basic-bitch-foundation/HUGINN/images/videoframe_134466 (1).png

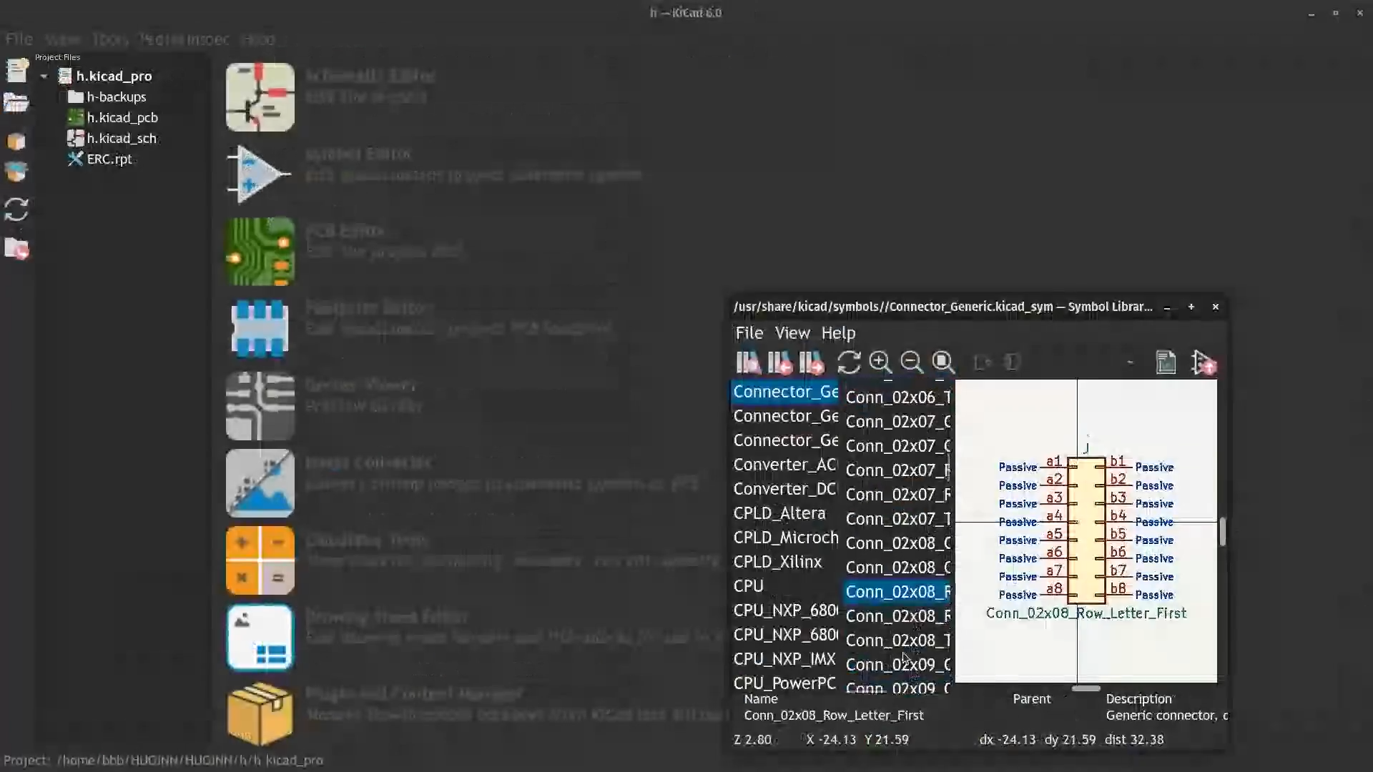
images/videoframe_134466 (1).png
