basic-bitch-foundation/HUGINN/images/videoframe_507285.png

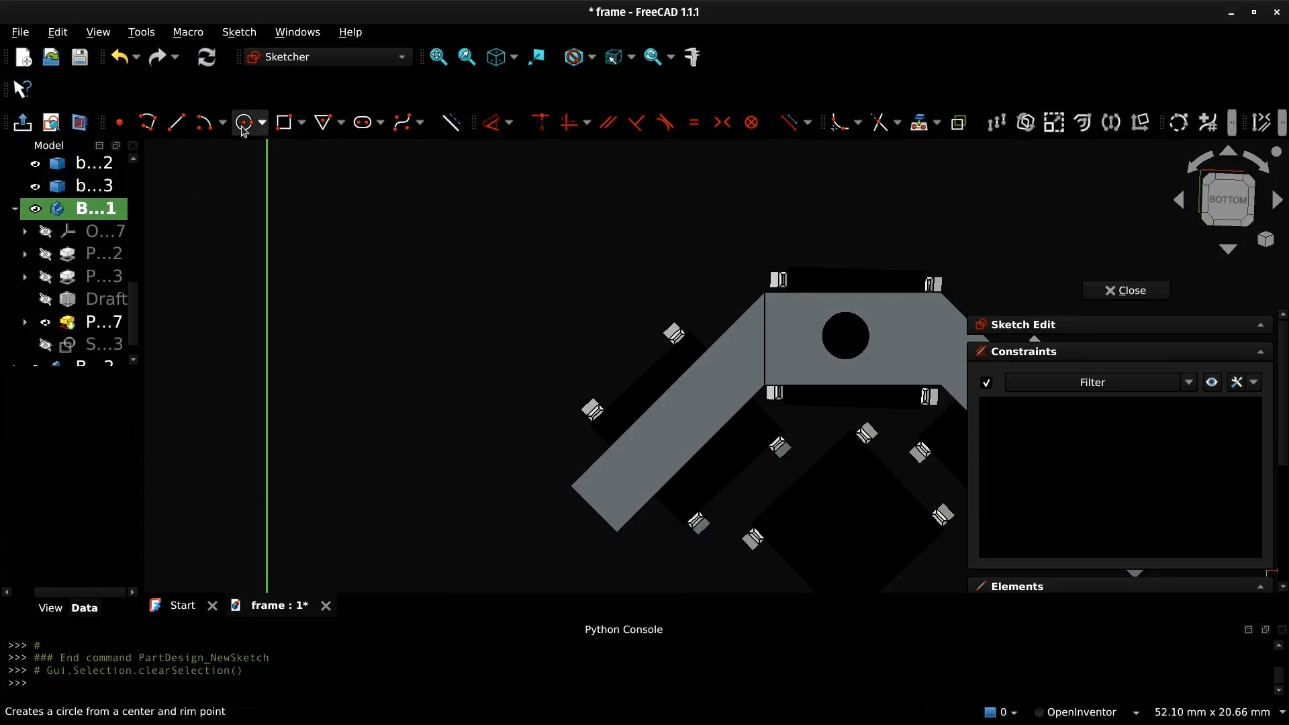
images/videoframe_507285.png
